Developer-Vini/keyboard/docs/Images/mx_stap.png

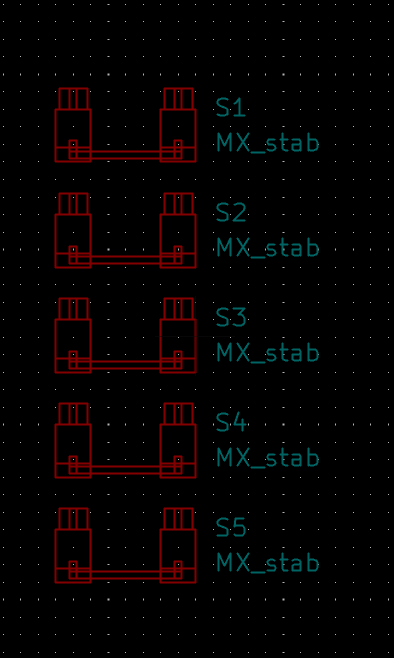
docs/Images/mx_stap.png
